Dr-schobi/smd-challenge/screenshots/IMG_20220904_204031101.jpg

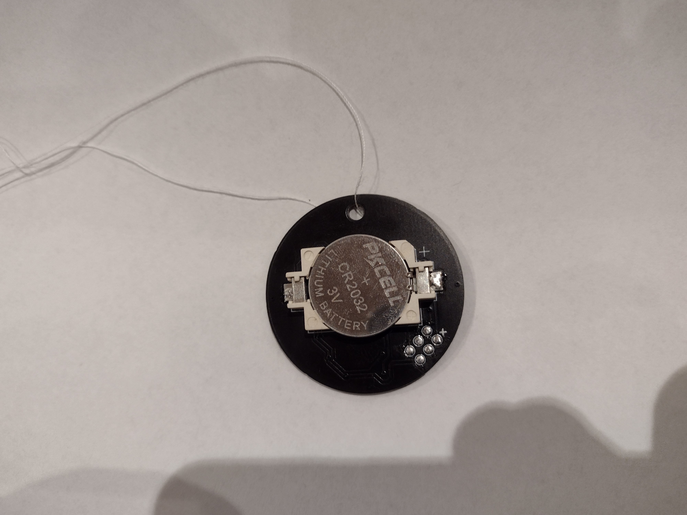
screenshots/IMG_20220904_204031101.jpg
