Dr-schobi/smd-challenge/screenshots/IMG_20220904_204101881.jpg

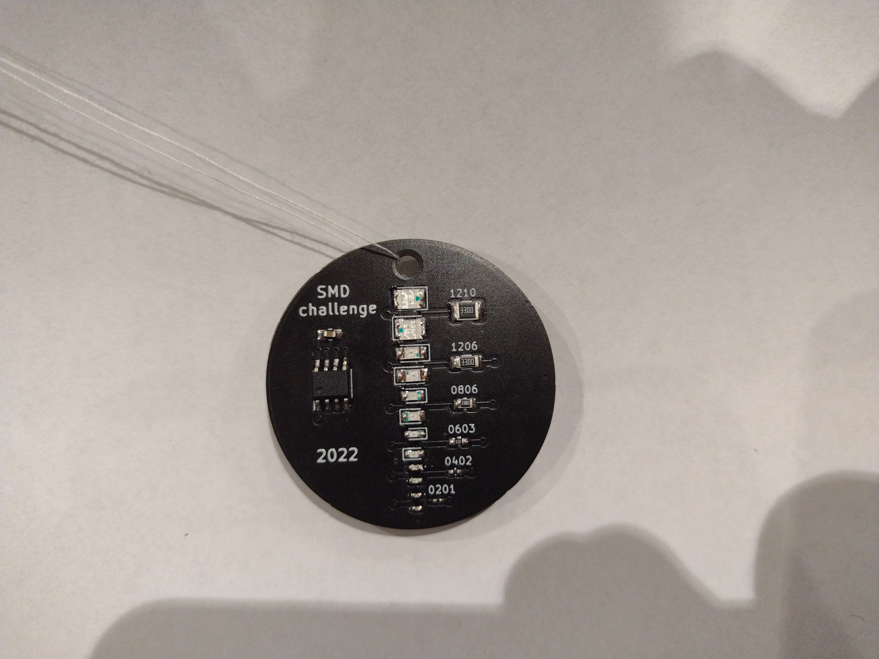
screenshots/IMG_20220904_204101881.jpg
