Dr-schobi/smd-challenge/screenshots/IMG_20220904_204820867.jpg

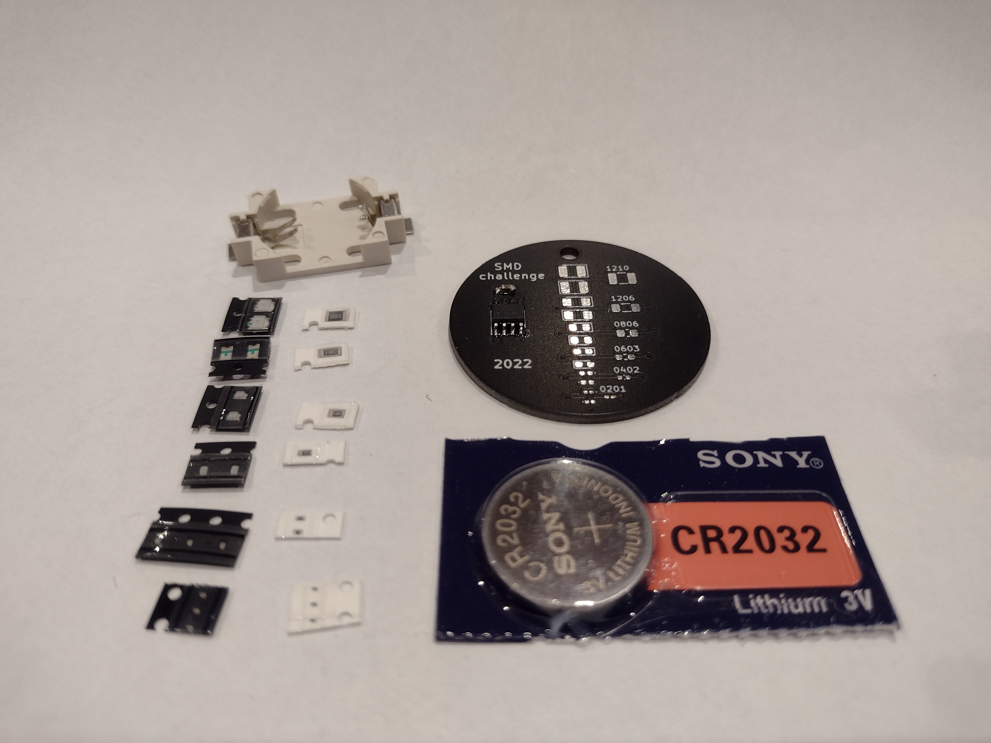
screenshots/IMG_20220904_204820867.jpg
